maxmacstn/HA-ePaper-Display/images/IMG_3539.jpg

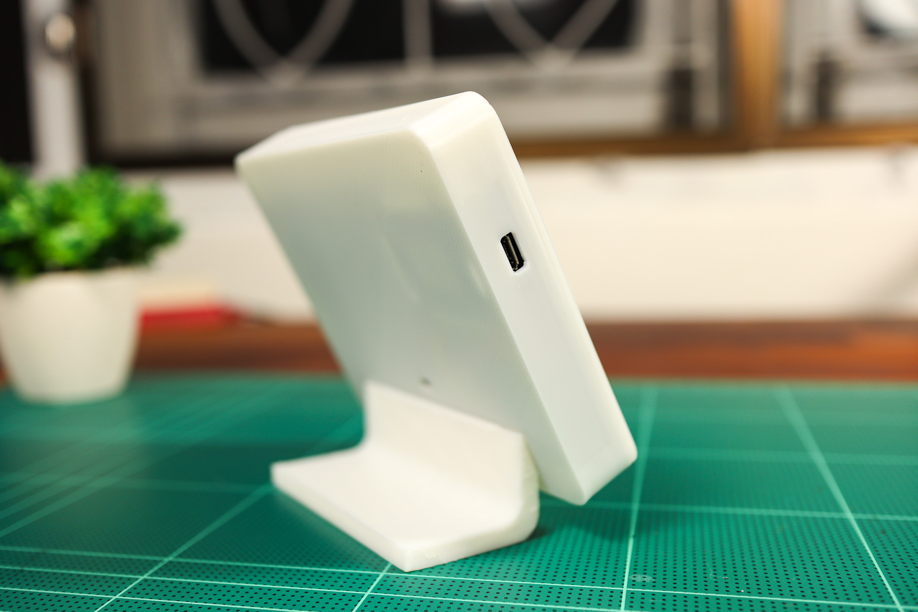
images/IMG_3539.jpg
