maxmacstn/HA-ePaper-Display/images/IMG_3540.jpg

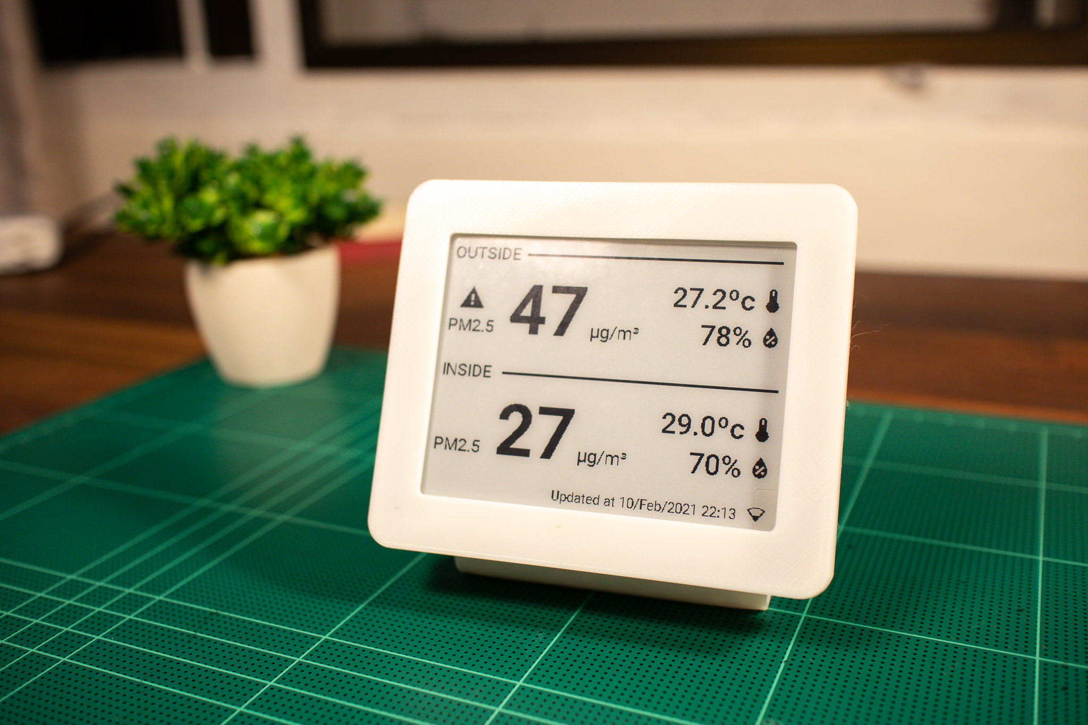
images/IMG_3540.jpg
