maxmacstn/HA-ePaper-Display/images/IMG_3542.jpg

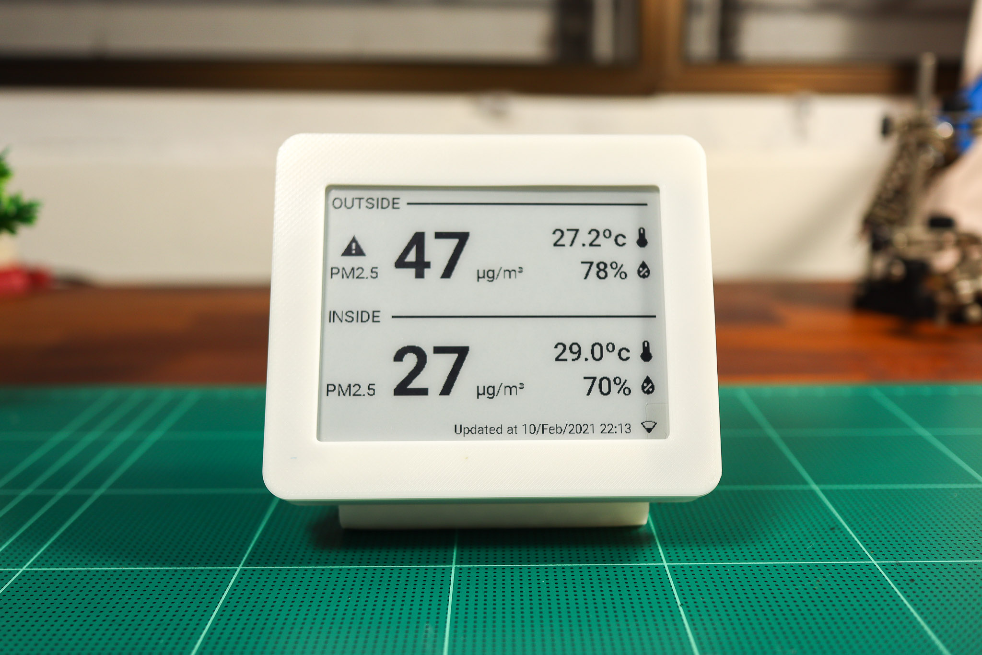
images/IMG_3542.jpg
