maxmacstn/HA-ePaper-Display/images/IMG_3543.jpg

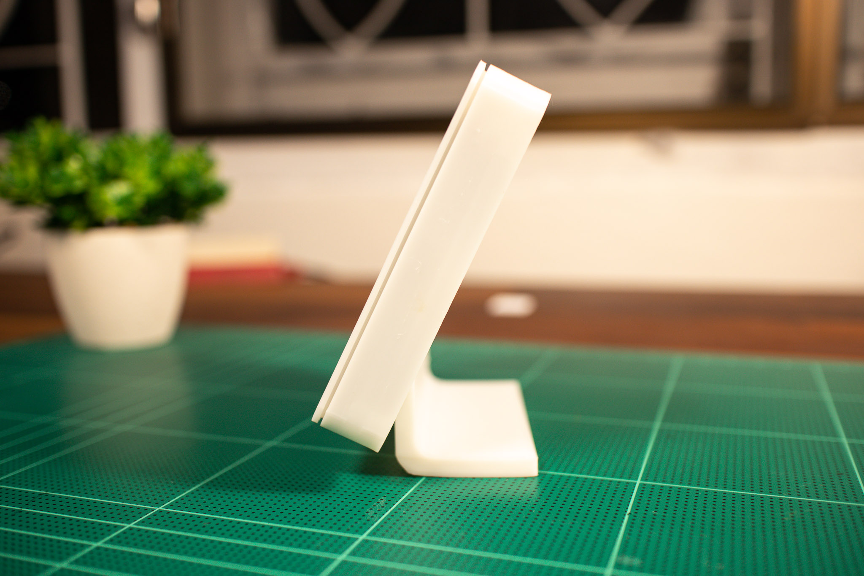
images/IMG_3543.jpg
