maxmacstn/HA-ePaper-Display/images/IMG_3547.jpg

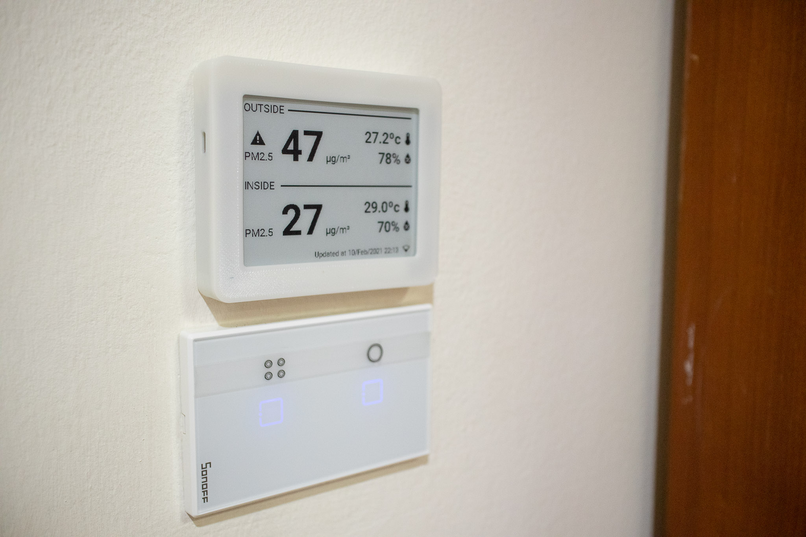
images/IMG_3547.jpg
