maxmacstn/HA-ePaper-Display/images/IMG_5575.jpg

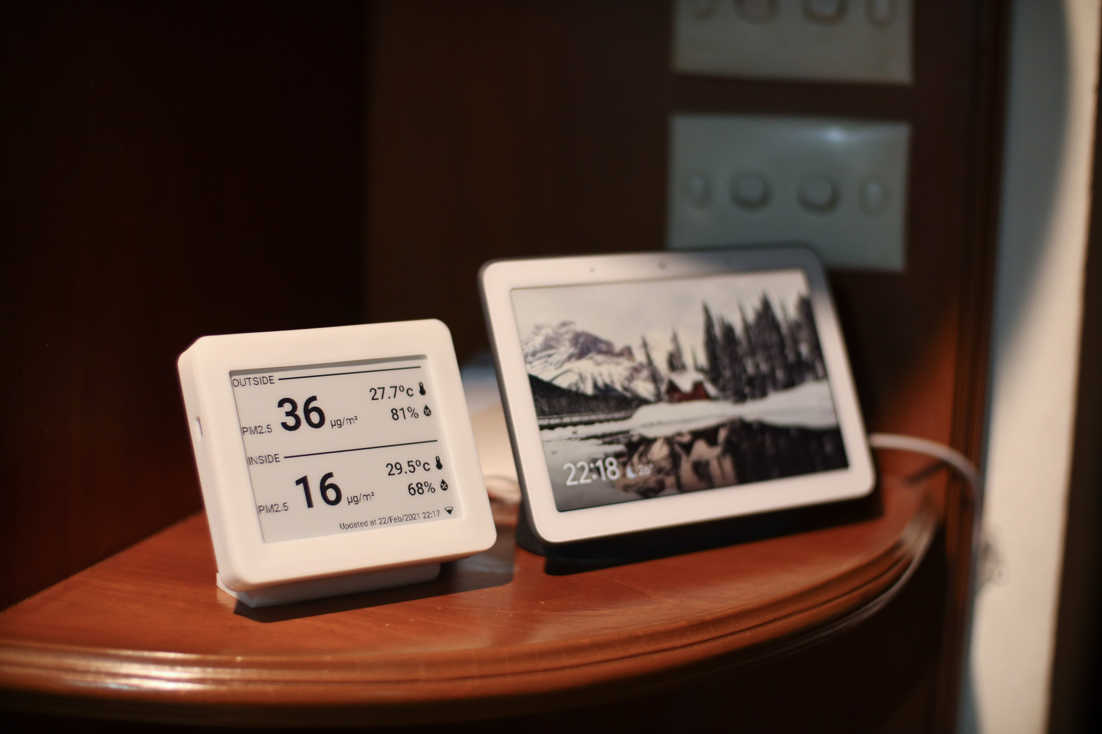
images/IMG_5575.jpg
